backtail/6hp-psu/LTSpice/Draft3.asc

D1: LED; NSSWS108T
D2: LED; NSSWS108T
D3: LED; NSSWS108T
R1: res; 8k2
R2: res; 8k2
R3: res; 2k2
V1: voltage; 12
V2: voltage; -12
V3: voltage; 5
Named nets: 0, +12V, -12V, +5V
.tran 1
