backtail/6hp-psu/LTSpice/Eurorack PSU.asc

C1: cap; 10n
C2: polcap; 1000µ; V=16 Irms=700m Rser=0.12 Lser=0 mfg="Nichicon" pn="UPR1C102MPH" type="Al electrolytic"
C3: polcap; 100µ; V=50 Irms=3.3m Rser=3.09403 Lser=3.75607n mfg="Würth Elektronik" pn="860010672001 WCAP-ATG8 5x11" type="Al electrolytic"
D1: schottky; MBR745
I1: load; 100m
L1: ind; 33µ; Ipk=3.5 Rser=0.078 Rpar=0 Cpar=0 mfg="Murata" pn="DD1274AS-H-330M=P3"
R1: res; 10k
R2: res; 10k
R3: res; 1k
R5: res; 10k
U1: LT1074
V1: voltage; 20; Rser=1m
Named nets: 0
.tran 10m startup
