backtail/6hp-psu/LTSpice/LM2596_05_In12V_Out5V3A.asc

C1: cap; 6µ
Cin: polcap; 680µ; V=25 Irms=1.27 Rser=0.055 Lser=0 mfg="Nichicon" pn="UPL1E681MRH6" type="Al electrolytic"
Cout: polcap; 220µ; V=16 Irms=460m Rser=0.16 Lser=0 mfg="Nichicon" pn="UPL1C221MPH" type="Al electrolytic"
D1: schottky; 1N5824
L1: ind; 38µ; Ipk=3 Rser=50m Cpar=0
L2: ind; 3µ
R3: res; 0.001
R4: res; 0.02
R5: res; 0.02
RLOAD: res; {RL}
U1: LM2596xx; LM2596_05
V1: battery; {Vin}; Rser=0.100
Named nets: 0, OUTPUT, +VIN, OUT, BAT
.tran 2m startup
.step param IOut 500m 3000m 500m
*.step param VIn 10 14 2
.ic I(L1)=0
.inc LM2596xx.txt
.options plotwinsize=0
.param VIn=12
.param VOut=5
.param IOut=320m
.param RL={VOut/IOUT}
10-14v
Inrush Input Fliter Model
.meas RLx param RL
.inc 1n582x.txt
TI LM2596-xx Fixed Output Regulator
SIMPLE SWITCHER Power Converter 150 KHz 3A Step-Down Voltage Regulator
UNREGULATED
DC INPUT
REGULATED OUTPUT
eetech00@yahoo.com
Mar 16 2015
