backtail/6hp-psu/LTSpice/LM2596ADJ_In12V_Out5V3A.asc

C1: cap; 0.1µ; V=25 Irms=0 Rser=0.035 Lser=765.574p mfg="Würth Elektronik" pn="885012205085 WCAP-CSGP 0402" type="X7R"
C2: cap; 0.1µ; V=25 Irms=0 Rser=0.035 Lser=765.574p mfg="Würth Elektronik" pn="885012205085 WCAP-CSGP 0402" type="X7R"
C3: cap; 0.1µ; V=25 Irms=0 Rser=0.035 Lser=765.574p mfg="Würth Elektronik" pn="885012205085 WCAP-CSGP 0402" type="X7R"
C4: cap; 0.1µ; V=25 Irms=0 Rser=0.035 Lser=765.574p mfg="Würth Elektronik" pn="885012205085 WCAP-CSGP 0402" type="X7R"
C5: cap; 0.1µ; V=25 Irms=0 Rser=0.035 Lser=765.574p mfg="Würth Elektronik" pn="885012205085 WCAP-CSGP 0402" type="X7R"
C6: cap; 0.1µ; V=25 Irms=0 Rser=0.035 Lser=765.574p mfg="Würth Elektronik" pn="885012205085 WCAP-CSGP 0402" type="X7R"
C7: cap; 10n
C8: cap; 10n
C9: cap; 10n
Cff1: cap; 22n; V=50 Irms=0 Rser=0 Lser=0
Cff: cap; 47n; V=50 Irms=0 Rser=0 Lser=0
Cin1: polcap; 200µ; V=26 Irms=3.87 Rser=0.002 Lser=0
Cin2: polcap; 200µ; V=26 Irms=3.87 Rser=0.002 Lser=0
Cin: polcap; 200µ; V=26 Irms=3.87 Rser=0.002 Lser=0
Cout1: polcap; 220µ; V=10 Irms=670m Rser=0.09 Lser=0
Cout2: polcap; 220µ; V=10 Irms=670m Rser=0.09 Lser=0
Cout3: cap; 10µ; V=16 Irms=0 Rser=0.00377815 Lser=877.331p mfg="Würth Elektronik" pn="885012108017 WCAP-CSGP 1206" type="X5R"
Cout4: cap; 10µ; V=16 Irms=0 Rser=0.00377815 Lser=877.331p mfg="Würth Elektronik" pn="885012108017 WCAP-CSGP 1206" type="X5R"
Cout5: cap; 10µ; V=16 Irms=0 Rser=0.00377815 Lser=877.331p mfg="Würth Elektronik" pn="885012108017 WCAP-CSGP 1206" type="X5R"
Cout: polcap; 220µ; V=10 Irms=670m Rser=0.09 Lser=0
D1: schottky; DI_B340A
D2: schottky; DI_B340A
D3: schottky; DI_B340A
L1: ind; 33µ; Ipk=3.0 Rser=0.033 Rpar=3108.6 Cpar=0
L2: ind; 33µ; Ipk=6.9 Rser=0.033 Rpar=3108.6 Cpar=0
L3: ind; 33µ; Ipk=6.9 Rser=0.033 Rpar=3108.6 Cpar=0
R1: res; 1k2
R2: res; 6k2
R3: res; 1k2
R4: res; 15k
R5: res; 1k
R6: res; 11k
R7: res; 15
R8: res; 5
R9: res; 10
R10: res; 47k
R11: res; 47k
R12: res; 47k
R13: res; 47k
R14: res; 47k
R15: res; 47k
U1: LM2596xx
U2: Vreg; LM7812
U3: LM2596xx
U4: Vreg; LM7912
U5: LM2596xx
U6: Vreg; LM7805
V1: battery; 15; Rser=100m
Named nets: 0
.tran 6m startup
.inc B340A.txt
.inc LM2596xx.txt
.lib regulators.lib
LM7805
LM7812
LM7912
